telzo2000/cool936tb2/img/img00003.jpg

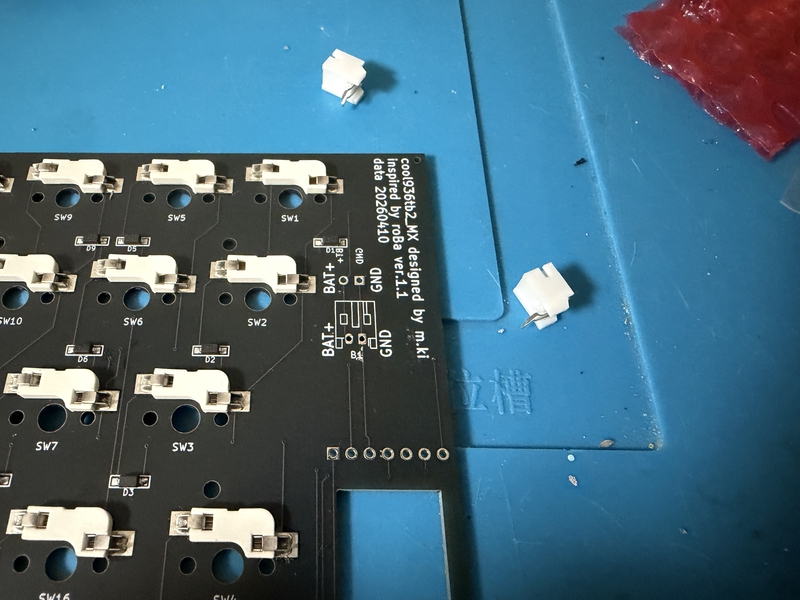
img/img00003.jpg
