telzo2000/cool936tb2/img/img00004.jpg

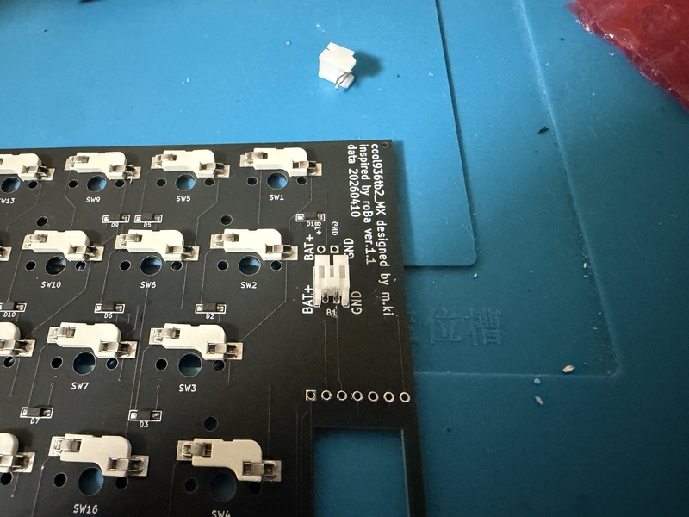
img/img00004.jpg
