telzo2000/cool936tb2/img/img00005.jpg

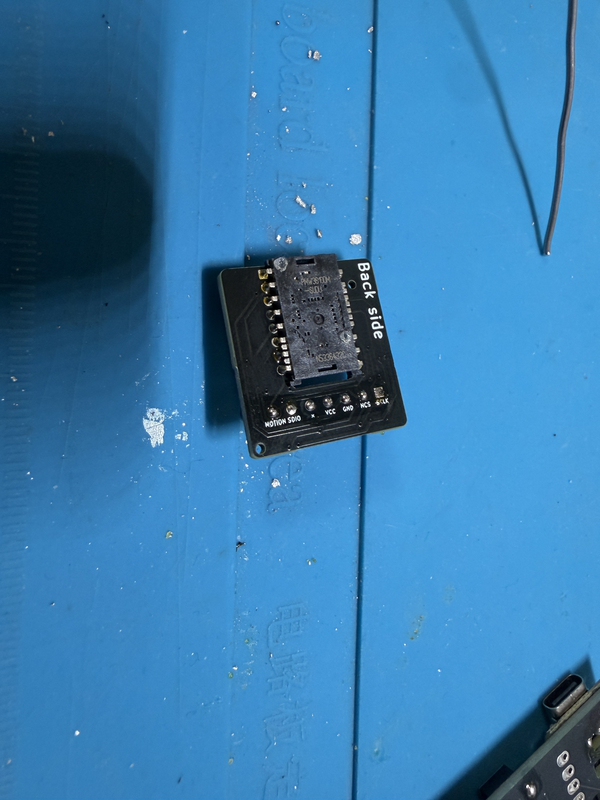
img/img00005.jpg
